madelinegannon/jetson-nano-accessories/stands/jetson_nano_clip-feet-battery.stl

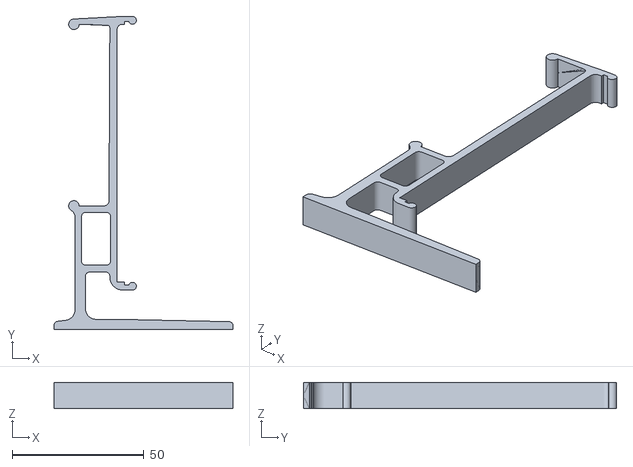
[picture p38: CAD file, 2019-06-07]
stands/jetson_nano_clip-feet-battery.stl
68.0 x 119.0 x 10.0
