madelinegannon/jetson-nano-accessories/utility-belt/jetson_nano_board_buckle.stl

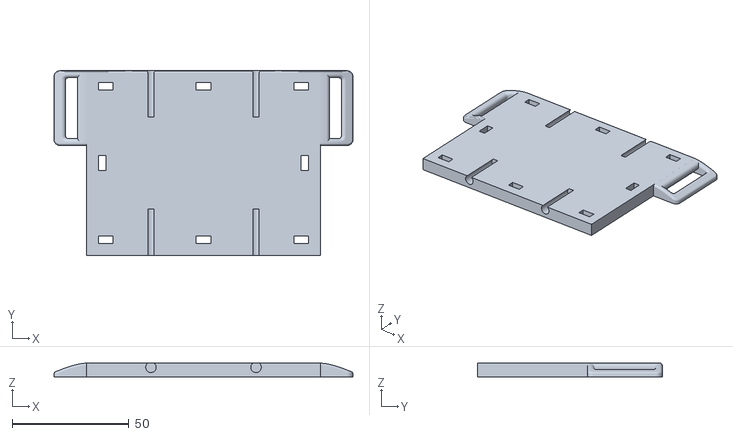
[picture p39: CAD file, 2019-06-04]
utility-belt/jetson_nano_board_buckle.stl
128.0 x 79.0 x 6.00
