madelinegannon/jetson-nano-accessories/gardening/jetson_nano_clip.stl

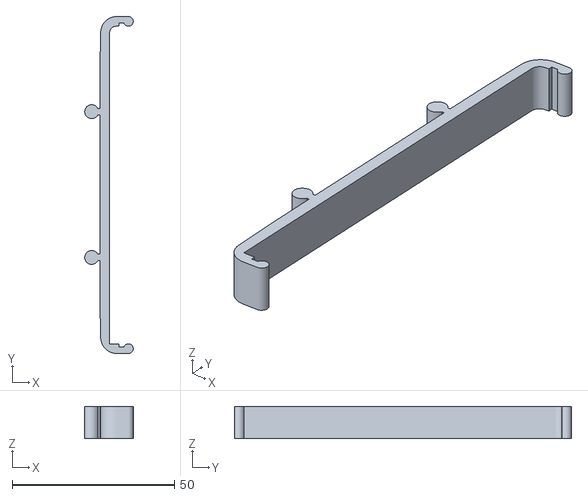
[picture p40: CAD file, 2019-06-04]
gardening/jetson_nano_clip.stl
15.0 x 104.0 x 10.0
